InaneCoding/KOS01_IdealDiode20A/sims/ideal_diode_simulation.asc

C1: cap; 2µ2
C2: cap; 100µ
I1: load; SINE(10.1 9.9 10); AC 1 0
L1: ind; 1f
L2: ind; 1f
M1: nmos; BSC028N06LS3
M3: nmos; IPT004N03L
R1: res; 3k6
R3: res; 0.6
U1: LTC4359
V1: voltage; 55v; Rser=0.01
V2: voltage; PULSE(0 15 0.01 10p 10p 0.005); Rser=0 Cpar=0
Named nets: 0, IN, OUT, GATE, VSS, SOURCE
.tran 0 0.02 0 1u
